Siliconinsid/SCSIknife/schematics/SCSIknife.kicad_sch

## KiCad design schematics/SCSIknife.kicad_sch (2025-09-15)

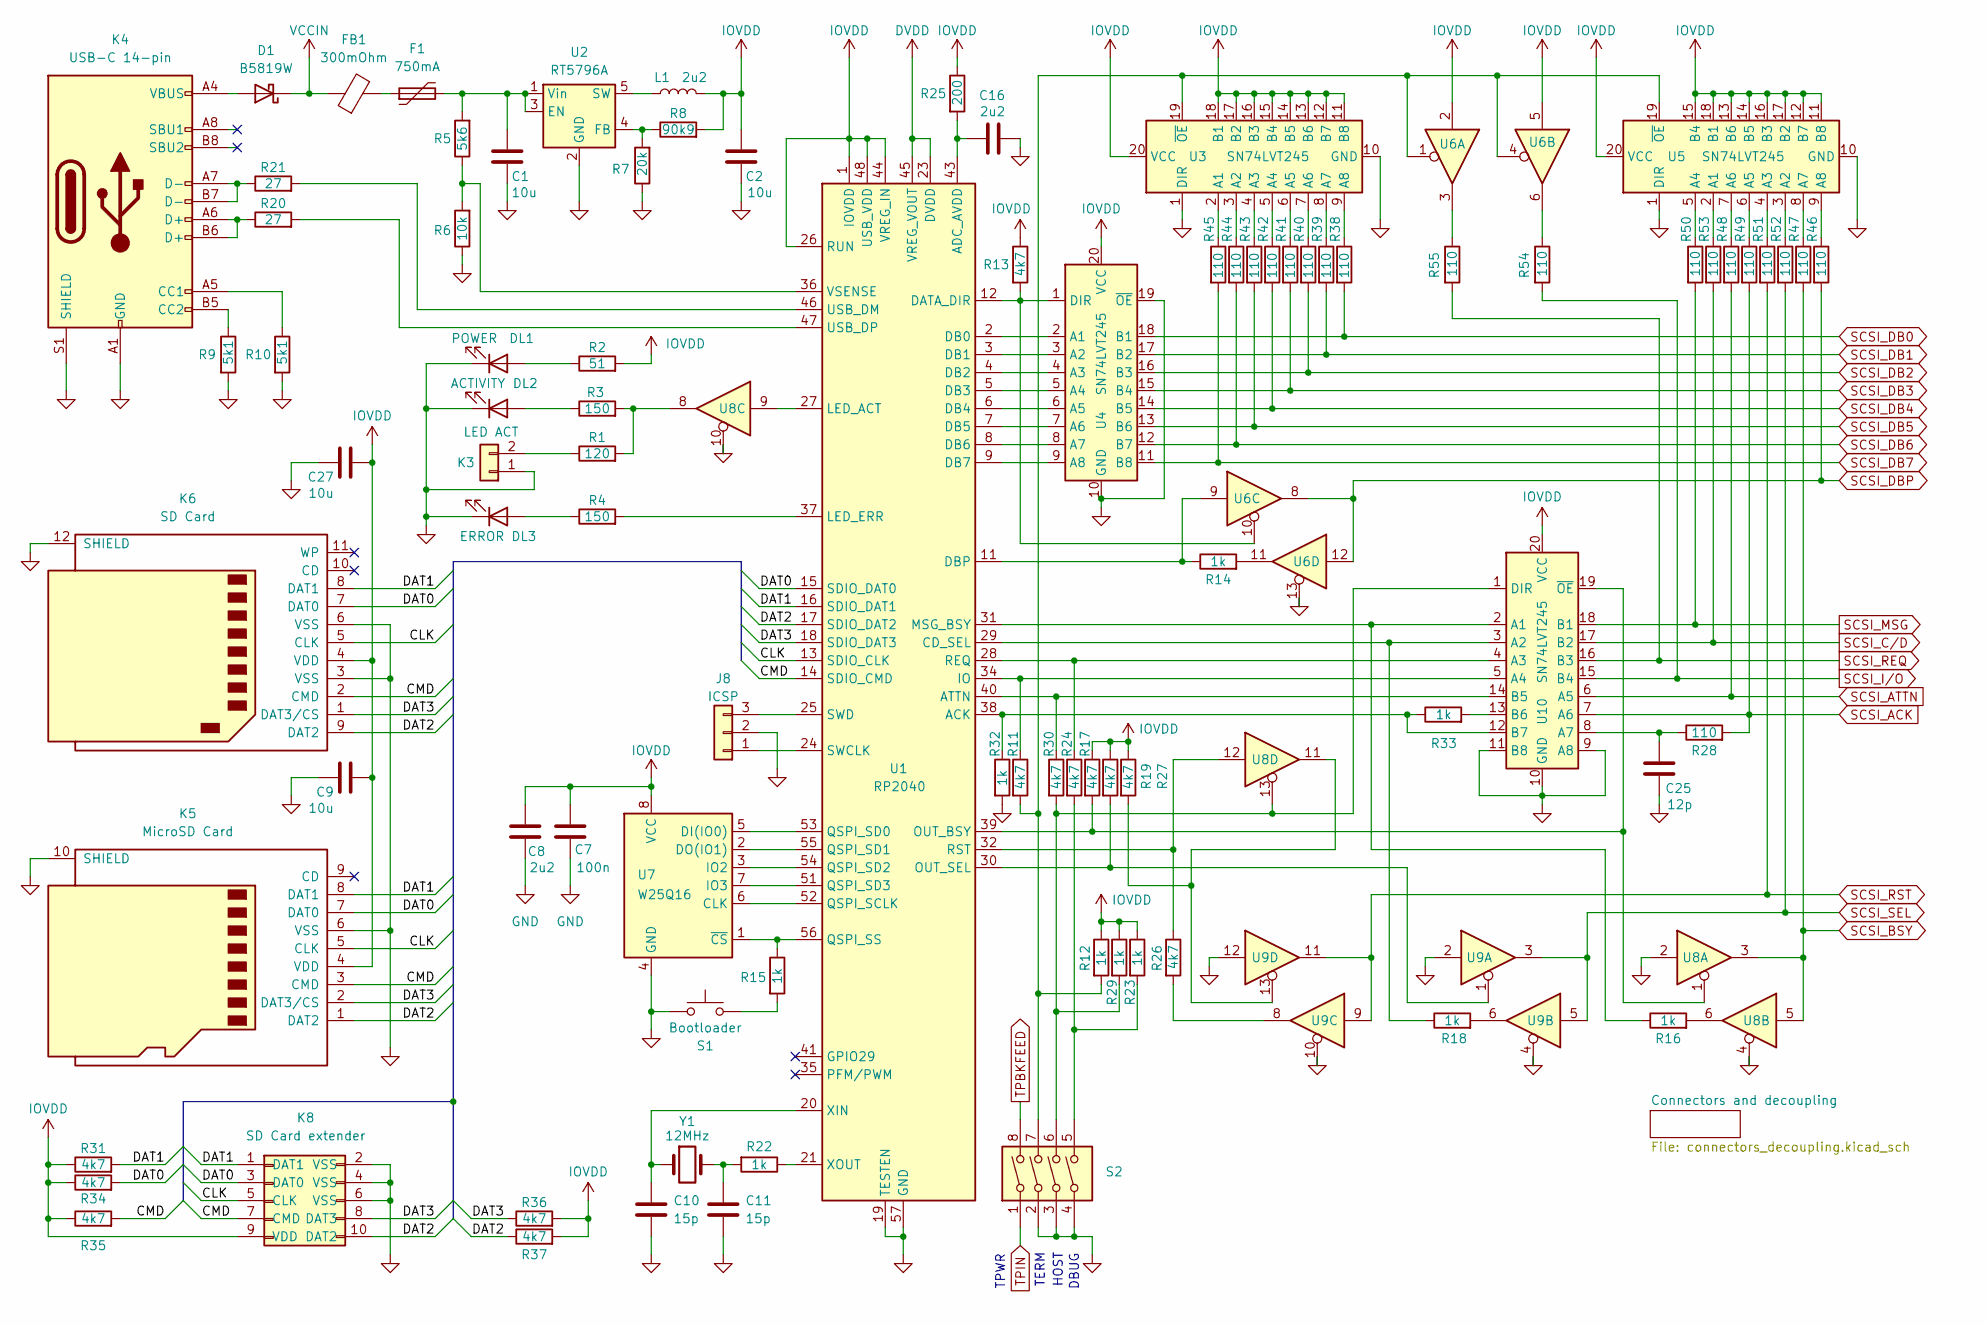
[picture p5: schematic SCSIknife.kicad_sch]

Parts:
C1, C2, C9, C27: 10u
C7: 100n
C8, C16: 2u2
C10, C11: 15p
C25: 12p
D1: B5819W; D_DO-41_SOD81_P10.16mm_Horizontal
DL1: POWER
DL2: ACTIVITY
DL3: ERROR
F1: 750mA
FB1: 300mOhm
J8: ICSP
K3: LED ACT
K4: USB-C 14-pin
K5: MicroSD Card
K6: SD Card
K8: SD Card extender
L1: 2u2
R1: 120
R2: 51
R3, R4: 150
R5: 5k6
R6: 10k
R7: 20k
R8: 90k9
R9, R10: 5k1
R11, R13, R17, R19, R24, R26, R27, R30, R31, R34, R35, R36, R37: 4k7
R12, R14, R15, R16, R18, R22, R23, R29, R32, R33: 1k
R20, R21: 27
R25: 200
R28, R38, R39, R40, R41, R42, R43, R44, R45, R46, R47, R48, R49, R50, R51, R52, R53, R54, R55: 110
S1: Bootloader
S2: SW_DIP_x04
U1: RP2040; QFN-56-1EP_7x7mm_P0.4mm_EP3.2x3.2mm
U2: RT5796A; TSOT-23-5
U3, U4, U5, U10: SN74LVT245; TSSOP-20_4.4x6.5mm_P0.65mm
U6, U8, U9: 74LVT125
U7: W25Q16; SOIC-8_5.23x5.23mm_P1.27mm
Y1: 12MHz

Connections:
CLK: K5.5 (CLK), K6.5 (CLK), K8.5 (CLK), U1.13 (SDIO_CLK)
CMD: K5.3 (CMD), K6.2 (CMD), K8.7 (CMD), R35.2, U1.14 (SDIO_CMD)
DAT0: K5.7 (DAT0), K6.7 (DAT0), K8.3 (DAT0), R34.2, U1.15 (SDIO_DAT0)
DAT1: K5.8 (DAT1), K6.8 (DAT1), K8.1 (DAT1), R31.2, U1.16 (SDIO_DAT1)
DAT2: K5.1 (DAT2), K6.9 (DAT2), K8.10 (DAT2), R37.1, U1.17 (SDIO_DAT2)
DAT3: K5.2 (DAT3/CS), K6.1 (DAT3/CS), K8.8 (DAT3), R36.1, U1.18 (SDIO_DAT3)
DVDD: U1.23 (DVDD), U1.45 (VREG_VOUT), U1.50 (DVDD)
GND: C1.2, C2.2, C7.2, C8.2, C9.1, C10.2, C11.2, C16.2, C25.2, C27.1, DL1.1 (K), DL2.1 (K), DL3.1 (K), J8.2, K3.1, K4.A1 (GND), K4.A12 (GND), K4.B1 (GND), K4.B12 (GND), K4.S1 (SHIELD), K5.6 (VSS), K5.10 (SHIELD), K6.3 (VSS), K6.6 (VSS), K6.12 (SHIELD), K8.2 (VSS), K8.4 (VSS), K8.6 (VSS), R6.1, R7.1, R9.2, R10.2, R32.2, S1.1, S2.2, S2.3, S2.4, U1.19 (TESTEN), U1.57 (GND), U2.2 (GND), U3.1 (DIR), U3.10 (GND), U4.10 (GND), U4.19 (~OE), U5.1 (DIR), U5.10 (GND), U6.13, U7.4 (GND), U8.2, U8.4, U8.10, U9.2, U9.4, U9.10, U9.12, U10.9 (A8), U10.10 (GND), U10.11 (B8)
IOVDD: C2.1, C7.1, C8.1, C9.2, C27.2, K5.4 (VDD), K6.4 (VDD), K8.9 (VDD), L1.2, R2.2, R8.2, R12.1, R13.1, R17.1, R19.1, R23.1, R25.1, R27.1, R29.1, R31.1, R34.1, R35.1, R36.2, R37.2, U1.1 (IOVDD), U1.10 (IOVDD), U1.22 (IOVDD), U1.26 (RUN), U1.33 (IOVDD), U1.42 (IOVDD), U1.44 (VREG_IN), U1.48 (USB_VDD), U1.49 (IOVDD), U3.11 (B8), U3.12 (B7), U3.13 (B6), U3.14 (B5), U3.15 (B4), U3.16 (B3), U3.17 (B2), U3.18 (B1), U3.20 (VCC), U4.20 (VCC), U5.11 (B8), U5.12 (B7), U5.13 (B6), U5.14 (B5), U5.15 (B4), U5.16 (B3), U5.17 (B2), U5.18 (B1), U5.20 (VCC), U6.2, U6.5, U7.8 (VCC), U10.20 (VCC)
unnamed: C1.1, F1.2, R5.2, U2.1 (Vin), U2.3 (EN)
unnamed: C10.1, U1.20 (XIN), Y1.1
unnamed: C11.1, R22.2, Y1.2
unnamed: C16.1, R25.2, U1.43 (ADC_AVDD)
unnamed: C25.1, R28.1, U10.8 (A7)
unnamed: D1.2 (A), K4.A4 (VBUS), K4.A9 (VBUS), K4.B4 (VBUS), K4.B9 (VBUS)
unnamed: DL1.2 (A), R2.1
unnamed: DL2.2 (A), R3.1
unnamed: DL3.2 (A), R4.1
unnamed: F1.1, FB1.2
unnamed: J8.1, U1.24 (SWCLK)
unnamed: J8.3, U1.25 (SWD)
unnamed: K3.2, R1.1
unnamed: K4.A5 (CC1), R10.1
unnamed: K4.A6 (D+), K4.B6 (D+), R20.1
unnamed: K4.A7 (D-), K4.B7 (D-), R21.1
unnamed: K4.B5 (CC2), R9.1
unnamed: L1.1, U2.5 (SW)
unnamed: R1.2, R3.2, U8.8
unnamed: R4.2, U1.37 (LED_ERR)
unnamed: R5.1, R6.2, U1.36 (VSENSE)
unnamed: R7.2, R8.1, U2.4 (FB)
unnamed: R11.1, U1.34 (IO), U10.5 (A4)
unnamed: R11.2, R12.2, S2.7, U3.19 (~OE), U5.19 (~OE), U6.1, U6.4
unnamed: R13.2, U1.12 (DATA_DIR), U4.1 (DIR), U6.10
unnamed: R14.1, U1.11 (DBP), U6.9
unnamed: R14.2, U6.11
unnamed: R15.1, U1.56 (QSPI_SS), U7.1 (~CS)
unnamed: R15.2, S1.2
unnamed: R16.1, U1.31 (MSG_BSY), U10.2 (A1)
unnamed: R16.2, U8.6
unnamed: R17.2, U1.39 (OUT_BSY), U8.1, U10.19 (~OE)
unnamed: R18.1, U1.29 (CD_SEL), U10.3 (A2)
unnamed: R18.2, U9.6
unnamed: R19.2, U1.30 (OUT_SEL), U9.1
unnamed: R20.2, U1.47 (USB_DP)
unnamed: R21.2, U1.46 (USB_DM)
unnamed: R22.1, U1.21 (XOUT)
unnamed: R23.2, R24.2, S2.5
unnamed: R24.1, U1.28 (REQ), U10.4 (A3)
unnamed: R26.1, U1.32 (RST), U8.12
unnamed: R26.2, U9.8
unnamed: R27.2, U8.11, U9.13
unnamed: R29.2, R30.2, S2.6, U8.13, U10.1 (DIR)
unnamed: R30.1, U1.40 (ATTN), U10.14 (B5)
unnamed: R32.1, R33.1, U1.38 (ACK), U10.12 (B7)
unnamed: R33.2, U10.13 (B6)
unnamed: R38.1, U3.9 (A8)
unnamed: R39.1, U3.8 (A7)
unnamed: R40.1, U3.7 (A6)
unnamed: R41.1, U3.6 (A5)
unnamed: R42.1, U3.5 (A4)
unnamed: R43.1, U3.4 (A3)
unnamed: R44.1, U3.3 (A2)
unnamed: R45.1, U3.2 (A1)
unnamed: R46.1, U5.9 (A8)
unnamed: R47.1, U5.8 (A7)
unnamed: R48.1, U5.7 (A6)
unnamed: R49.1, U5.6 (A5)
unnamed: R50.1, U5.5 (A4)
unnamed: R51.1, U5.4 (A3)
unnamed: R52.1, U5.3 (A2)
unnamed: R53.1, U5.2 (A1)
unnamed: R54.1, U6.6
unnamed: R55.1, U6.3
unnamed: U1.2 (DB0), U4.2 (A1)
unnamed: U1.3 (DB1), U4.3 (A2)
unnamed: U1.4 (DB2), U4.4 (A3)
unnamed: U1.5 (DB3), U4.5 (A4)
unnamed: U1.6 (DB4), U4.6 (A5)
unnamed: U1.7 (DB5), U4.7 (A6)
unnamed: U1.8 (DB6), U4.8 (A7)
unnamed: U1.9 (DB7), U4.9 (A8)
unnamed: U1.27 (LED_ACT), U8.9
unnamed: U1.51 (QSPI_SD3), U7.7 (IO3)
unnamed: U1.52 (QSPI_SCLK), U7.6 (CLK)
unnamed: U1.53 (QSPI_SD0), U7.5 (DI(IO0))
unnamed: U1.54 (QSPI_SD2), U7.3 (IO2)
unnamed: U1.55 (QSPI_SD1), U7.2 (DO(IO1))
SCSI_ACK: R28.2, R49.2, U10.7 (A6)
SCSI_ATTN: R48.2, U10.6 (A5)
SCSI_BSY: R47.2, U8.3, U8.5
SCSI_C/D: R53.2, U10.17 (B2)
SCSI_DB0: R38.2, U4.18 (B1)
SCSI_DB1: R39.2, U4.17 (B2)
SCSI_DB2: R40.2, U4.16 (B3)
SCSI_DB3: R41.2, U4.15 (B4)
SCSI_DB4: R42.2, U4.14 (B5)
SCSI_DB5: R43.2, U4.13 (B6)
SCSI_DB6: R44.2, U4.12 (B7)
SCSI_DB7: R45.2, U4.11 (B8)
SCSI_DBP: R46.2, U6.8, U6.12
SCSI_I/O: R54.2, U10.15 (B4)
SCSI_MSG: R50.2, U10.18 (B1)
SCSI_REQ: R55.2, U10.16 (B3)
SCSI_RST: R51.2, U9.9, U9.11
SCSI_SEL: R52.2, U9.3, U9.5
TPBKFEED: S2.8
TPIN: S2.1
VCCIN: D1.1 (K), FB1.1

Notes on the sheet:
HOST
TERM
TPWR
DBUG
