Siliconinsid/SCSIknife/schematics/connectors_decoupling.kicad_sch

## KiCad design schematics/connectors_decoupling.kicad_sch (2024-12-31)

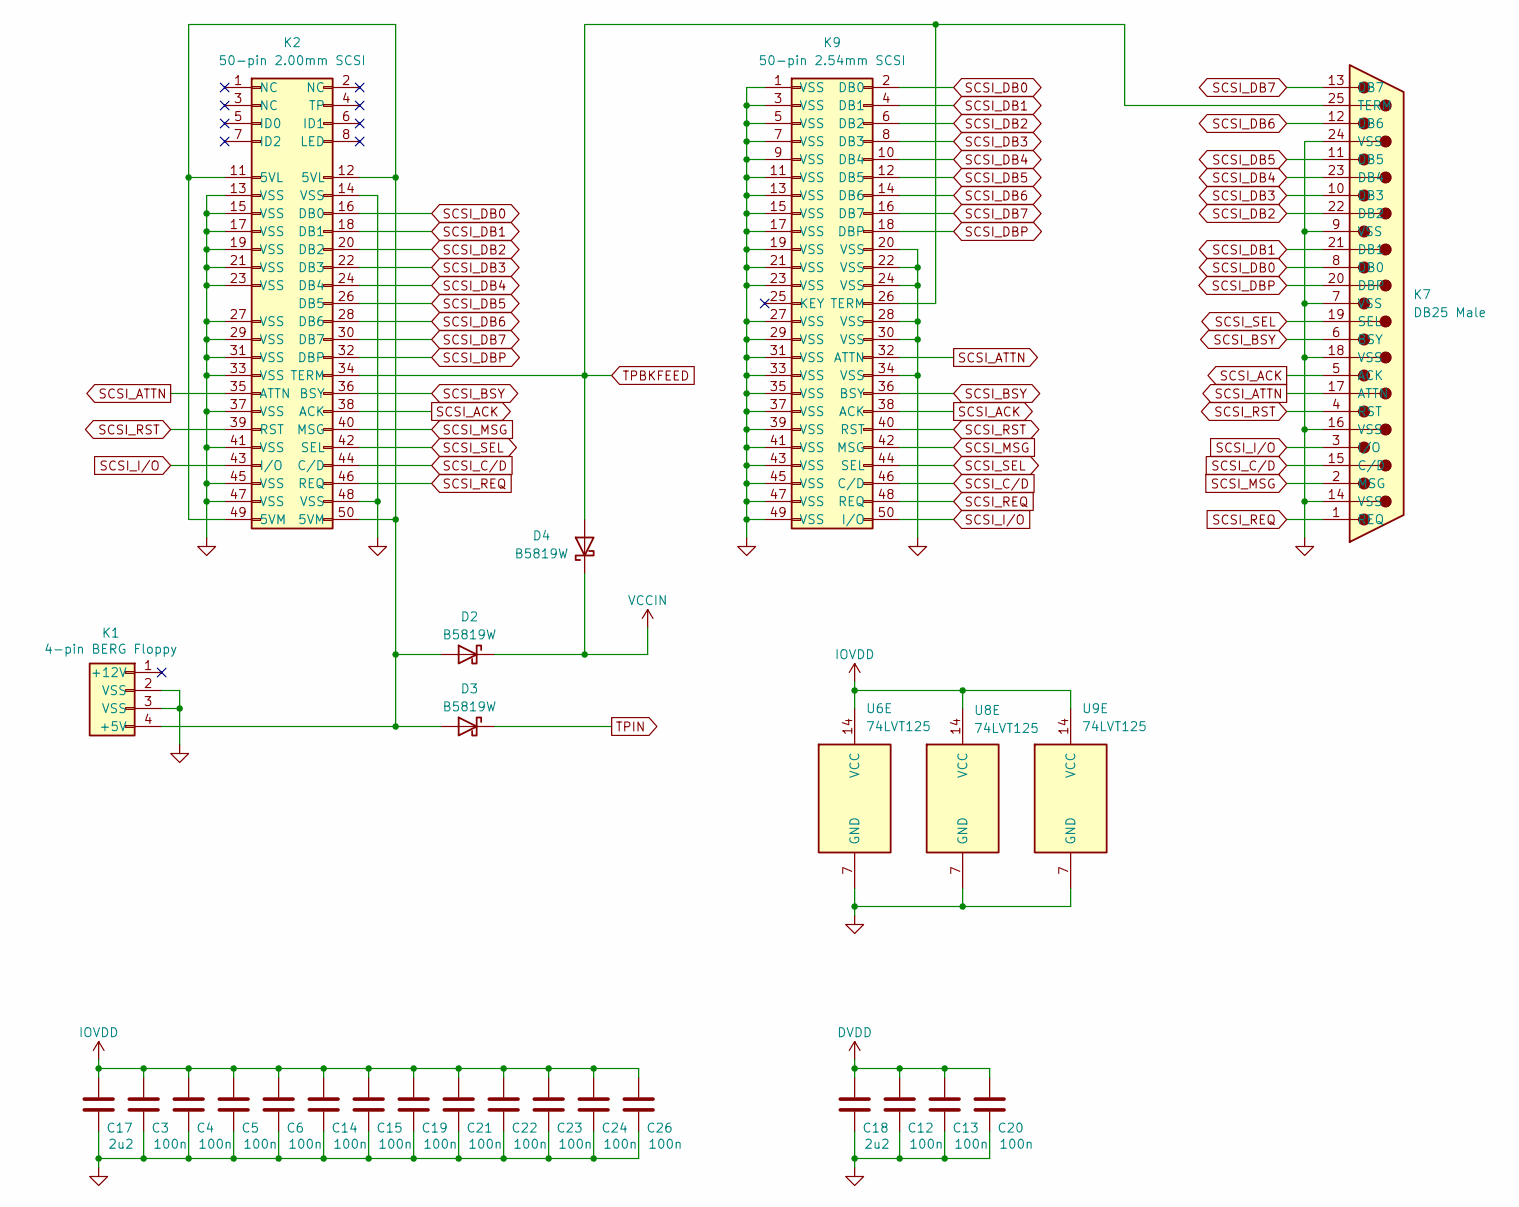
[picture p6: schematic connectors_decoupling.kicad_sch]

Parts:
C3, C4, C5, C6, C12, C13, C14, C15, C19, C20, C21, C22, C23, C24, C26: 100n
C17, C18: 2u2
D2, D3, D4: B5819W; D_DO-41_SOD81_P10.16mm_Horizontal
K1: 4-pin BERG Floppy
K2: 50-pin 2.00mm SCSI
K7: DB25 Male
K9: 50-pin 2.54mm SCSI
U6, U8, U9: 74LVT125

Connections:
DVDD: C12.1, C13.1, C18.1, C20.1
GND: C3.2, C4.2, C5.2, C6.2, C12.2, C13.2, C14.2, C15.2, C17.2, C18.2, C19.2, C20.2, C21.2, C22.2, C23.2, C24.2, C26.2, K1.2 (VSS), K1.3 (VSS), K2.13 (VSS), K2.14 (VSS), K2.15 (VSS), K2.17 (VSS), K2.19 (VSS), K2.21 (VSS), K2.23 (VSS), K2.27 (VSS), K2.29 (VSS), K2.31 (VSS), K2.33 (VSS), K2.37 (VSS), K2.41 (VSS), K2.45 (VSS), K2.47 (VSS), K2.48 (VSS), K7.7 (VSS), K7.9 (VSS), K7.14 (VSS), K7.16 (VSS), K7.18 (VSS), K7.24 (VSS), K9.1 (VSS), K9.3 (VSS), K9.5 (VSS), K9.7 (VSS), K9.9 (VSS), K9.11 (VSS), K9.13 (VSS), K9.15 (VSS), K9.17 (VSS), K9.19 (VSS), K9.20 (VSS), K9.21 (VSS), K9.22 (VSS), K9.23 (VSS), K9.24 (VSS), K9.27 (VSS), K9.28 (VSS), K9.29 (VSS), K9.30 (VSS), K9.31 (VSS), K9.33 (VSS), K9.34 (VSS), K9.35 (VSS), K9.37 (VSS), K9.39 (VSS), K9.41 (VSS), K9.43 (VSS), K9.45 (VSS), K9.47 (VSS), K9.49 (VSS), U6.7 (GND), U8.7 (GND), U9.7 (GND)
IOVDD: C3.1, C4.1, C5.1, C6.1, C14.1, C15.1, C17.1, C19.1, C21.1, C22.1, C23.1, C24.1, C26.1, U6.14 (VCC), U8.14 (VCC), U9.14 (VCC)
unnamed: D2.2 (A), D3.2 (A), K1.4 (+5V), K2.11 (5VL), K2.12 (5VL), K2.49 (5VM), K2.50 (5VM)
SCSI_ACK: K2.38 (ACK), K7.5 (ACK), K9.38 (ACK)
SCSI_ATTN: K2.35 (ATTN), K7.17 (ATTN), K9.32 (ATTN)
SCSI_BSY: K2.36 (BSY), K7.6 (BSY), K9.36 (BSY)
SCSI_C/D: K2.44 (C/D), K7.15 (C/D), K9.46 (C/D)
SCSI_DB0: K2.16 (DB0), K7.8 (DB0), K9.2 (DB0)
SCSI_DB1: K2.18 (DB1), K7.21 (DB1), K9.4 (DB1)
SCSI_DB2: K2.20 (DB2), K7.22 (DB2), K9.6 (DB2)
SCSI_DB3: K2.22 (DB3), K7.10 (DB3), K9.8 (DB3)
SCSI_DB4: K2.24 (DB4), K7.23 (DB4), K9.10 (DB4)
SCSI_DB5: K2.26 (DB5), K7.11 (DB5), K9.12 (DB5)
SCSI_DB6: K2.28 (DB6), K7.12 (DB6), K9.14 (DB6)
SCSI_DB7: K2.30 (DB7), K7.13 (DB7), K9.16 (DB7)
SCSI_DBP: K2.32 (DBP), K7.20 (DBP), K9.18 (DBP)
SCSI_I/O: K2.43 (I/O), K7.3 (I/O), K9.50 (I/O)
SCSI_MSG: K2.40 (MSG), K7.2 (MSG), K9.42 (MSG)
SCSI_REQ: K2.46 (REQ), K7.1 (REQ), K9.48 (REQ)
SCSI_RST: K2.39 (RST), K7.4 (RST), K9.40 (RST)
SCSI_SEL: K2.42 (SEL), K7.19 (SEL), K9.44 (SEL)
TPBKFEED: D4.2 (A), K2.34 (TERM), K7.25 (TERM), K9.26 (TERM)
TPIN: D3.1 (K)
VCCIN: D2.1 (K), D4.1 (K)
